srg74/WLED-wemos-shield/resources/Add-ons/ics-43434/ics43434_shield.jpg

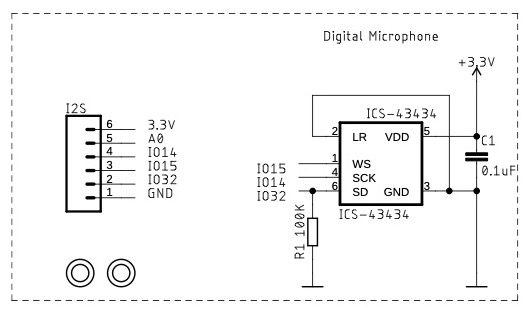
resources/Add-ons/ics-43434/ics43434_shield.jpg
