srg74/WLED-wemos-shield/resources/Add-ons/linear_input/Sound_reactive_add-on.png

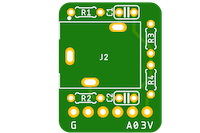
resources/Add-ons/linear_input/Sound_reactive_add-on.png
