srg74/WLED-wemos-shield/resources/Images/esp32-esp8266.jpg

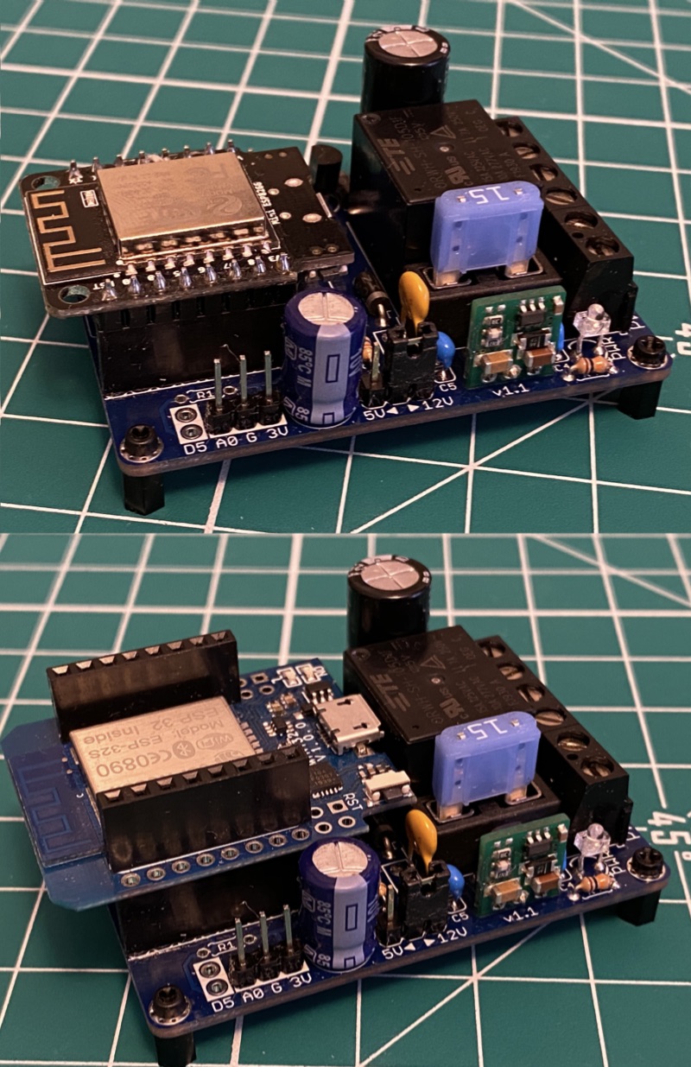
resources/Images/esp32-esp8266.jpg
