srg74/WLED-wemos-shield/resources/Images/ESP32_d1.jpeg

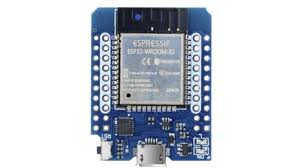
resources/Images/ESP32_d1.jpeg
