srg74/WLED-wemos-shield/resources/Images/Flasher1.png

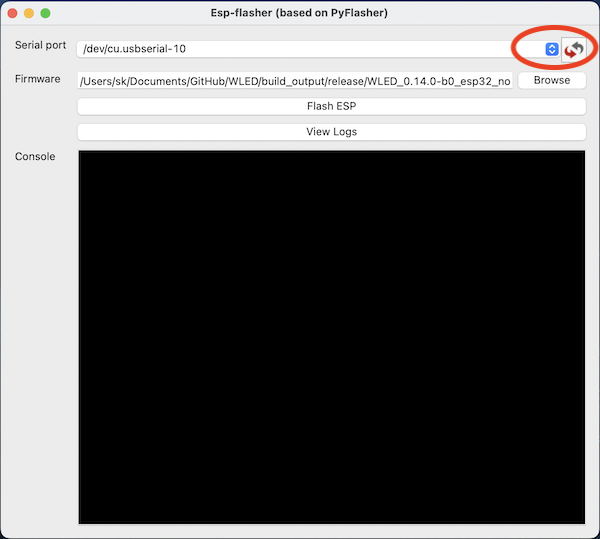
resources/Images/Flasher1.png
