srg74/WLED-wemos-shield/resources/Images/Flasher4.png

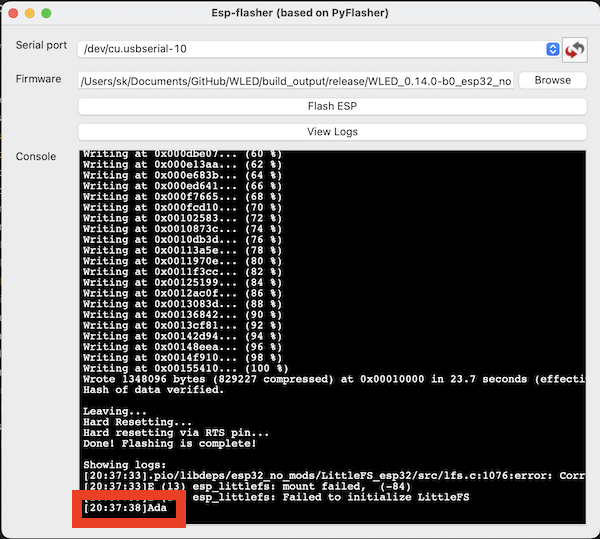
resources/Images/Flasher4.png
