srg74/WLED-wemos-shield/resources/Images/H803FW.jpg

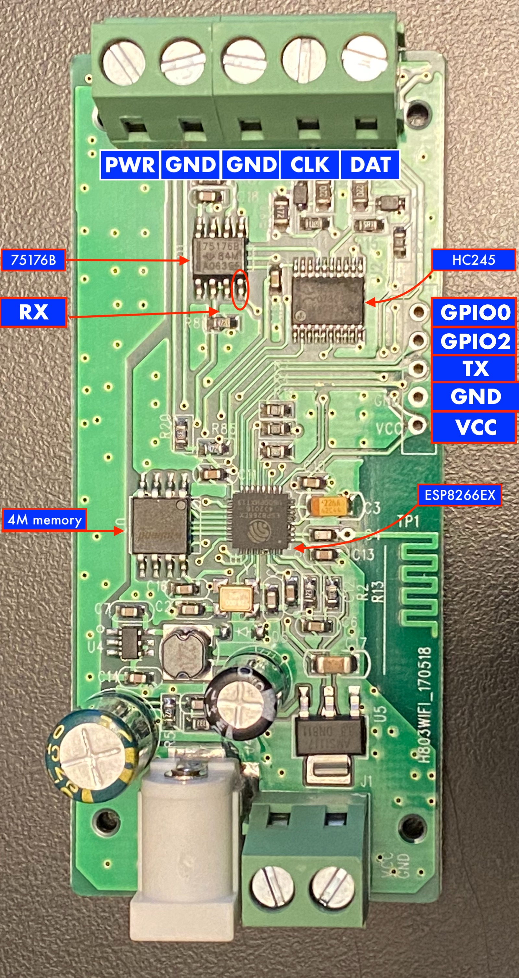
resources/Images/H803FW.jpg
