srg74/WLED-wemos-shield/resources/Images/Lilygo_TTGO_v1.3.jpeg

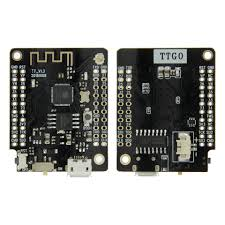
resources/Images/Lilygo_TTGO_v1.3.jpeg
