srg74/WLED-wemos-shield/resources/Images/mini.jpeg

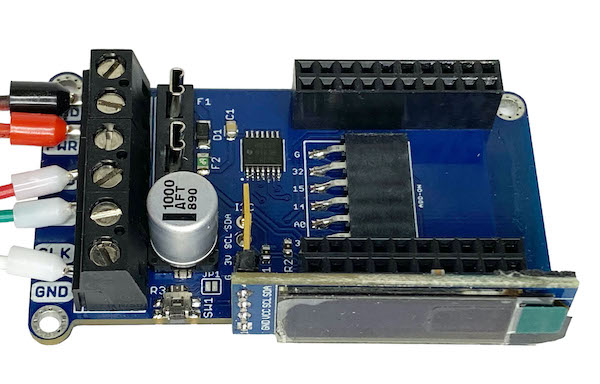
resources/Images/mini.jpeg
