srg74/WLED-wemos-shield/resources/Images/overview.jpg

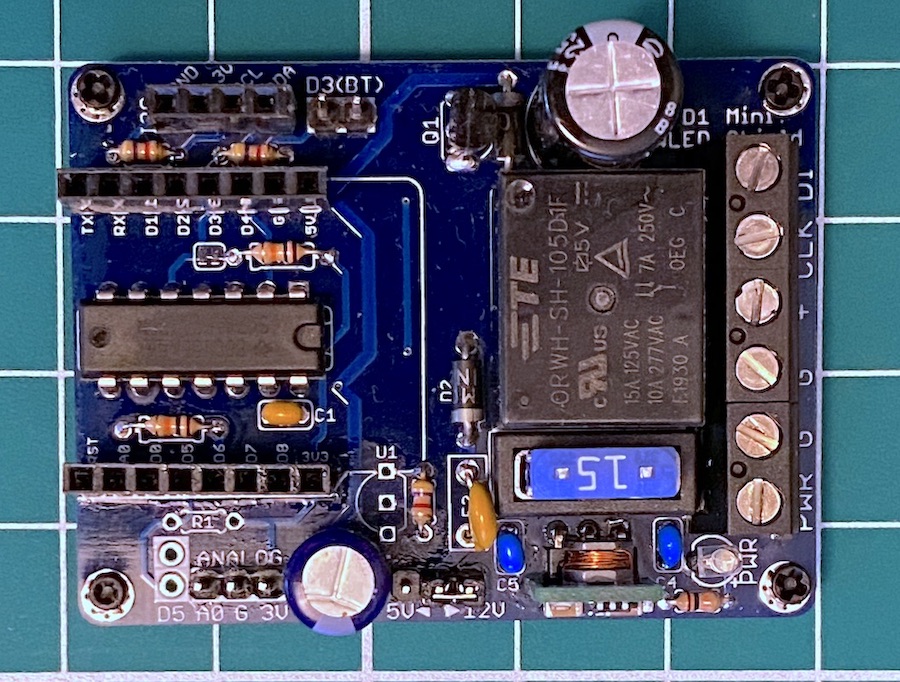
resources/Images/overview.jpg
