srg74/WLED-wemos-shield/resources/Images/Shield_v1.5-3D.png

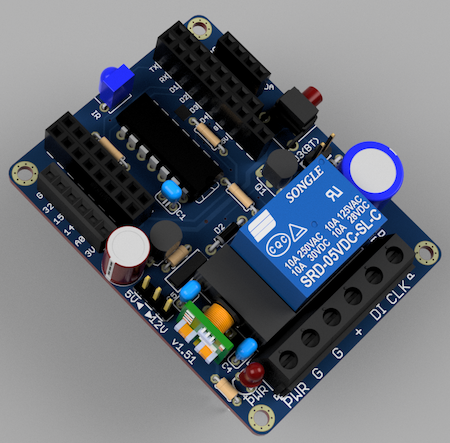
resources/Images/Shield_v1.5-3D.png
