srg74/WLED-wemos-shield/resources/Images/Variant_1.jpg

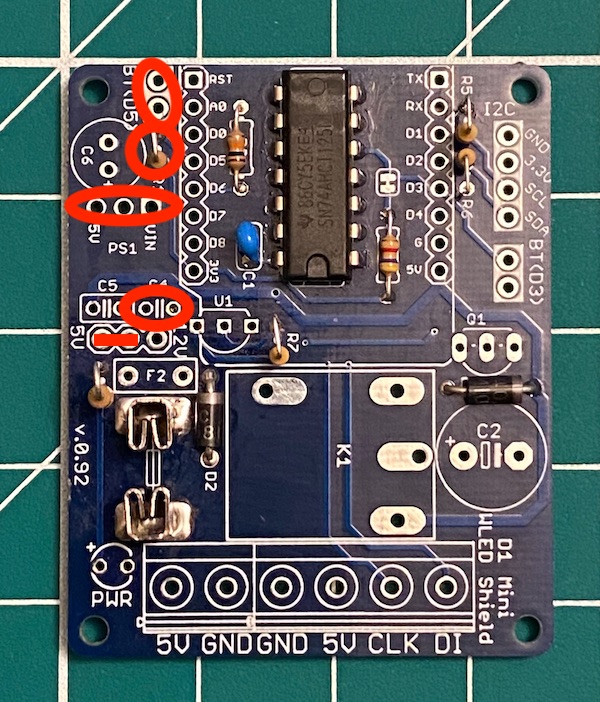
resources/Images/Variant_1.jpg
