srg74/WLED-wemos-shield/resources/Images/Variant_2.jpg

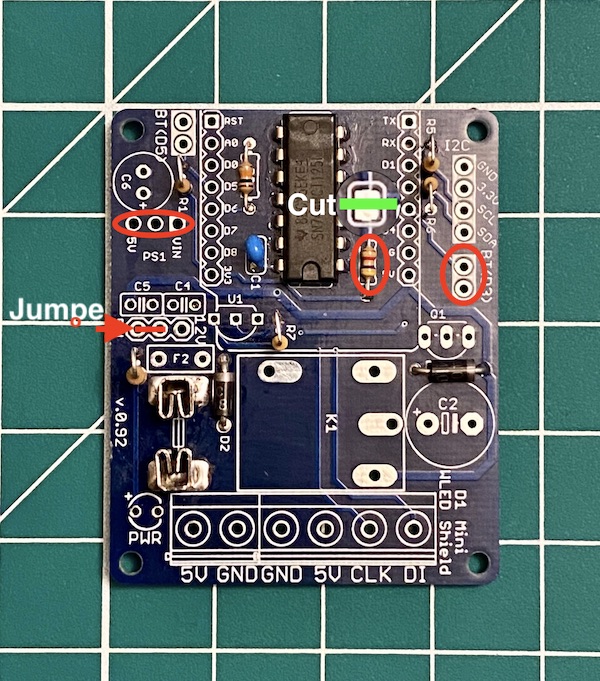
resources/Images/Variant_2.jpg
