srg74/WLED-wemos-shield/resources/Images/Variant_3.jpg

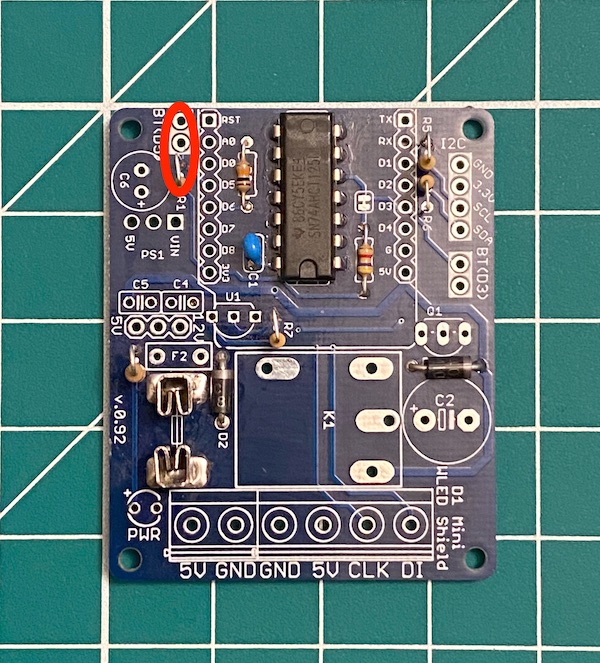
resources/Images/Variant_3.jpg
