srg74/WLED-wemos-shield/resources/Images/Wemos_clone.jpg

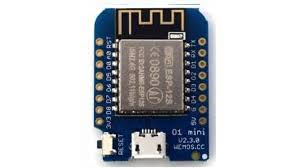
resources/Images/Wemos_clone.jpg
