srg74/WLED-wemos-shield/resources/Images/Wemos_orig.jpg

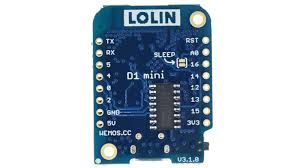
resources/Images/Wemos_orig.jpg
