srg74/WLED-wemos-shield/resources/Images/Wemos_set.jpg

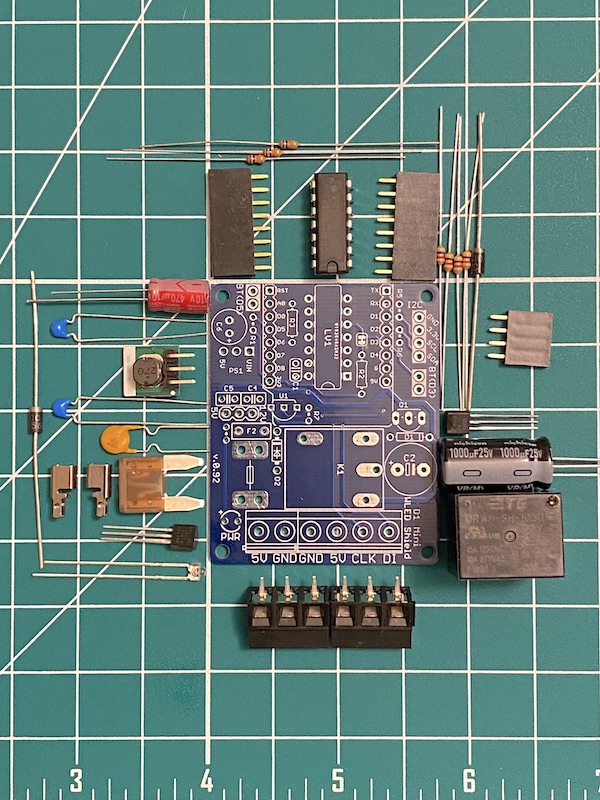
resources/Images/Wemos_set.jpg
