srg74/WLED-wemos-shield/resources/Images/wiki/board-powered.jpg

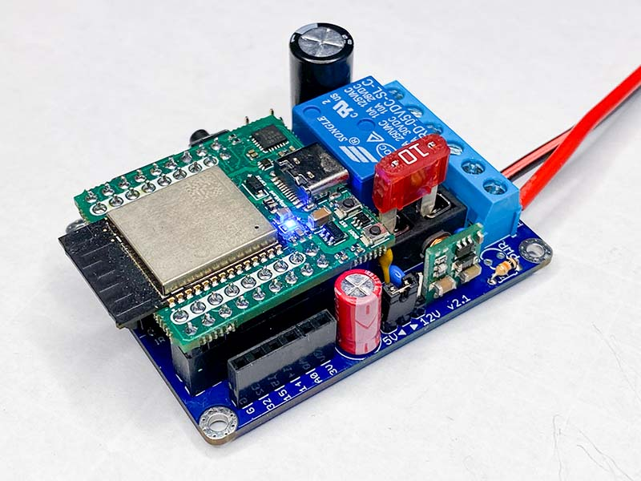
resources/Images/wiki/board-powered.jpg
