srg74/WLED-wemos-shield/resources/Images/wiki/board.jpg

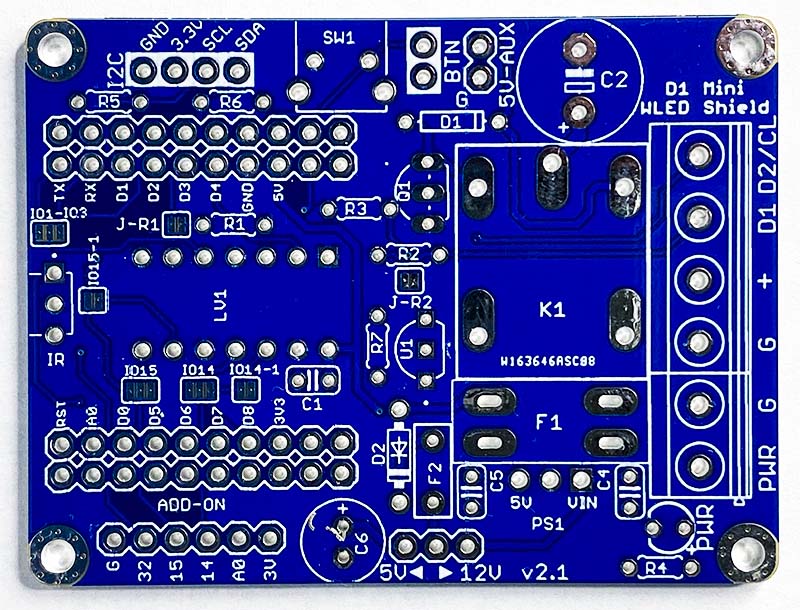
resources/Images/wiki/board.jpg
