srg74/WLED-wemos-shield/resources/Images/wiki/ESP32_mini_board1.png

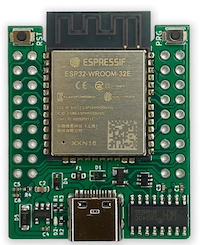
resources/Images/wiki/ESP32_mini_board1.png
