srg74/WLED-wemos-shield/resources/Images/wiki/jumper-set.jpg

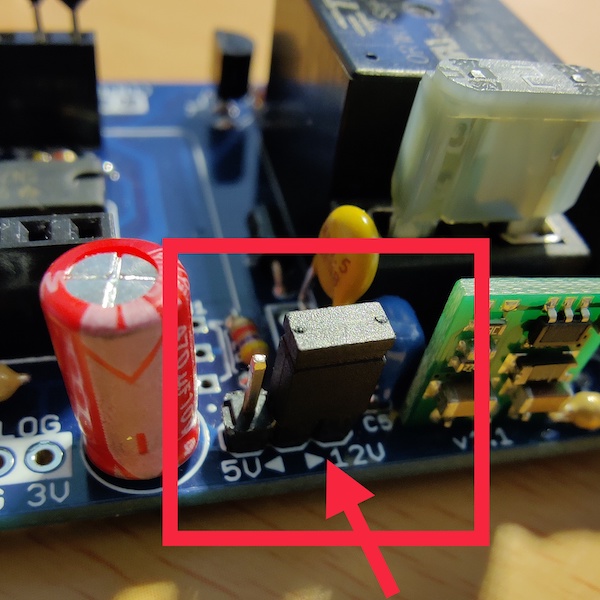
resources/Images/wiki/jumper-set.jpg
