srg74/WLED-wemos-shield/resources/Images/wiki/minimum-set.jpg

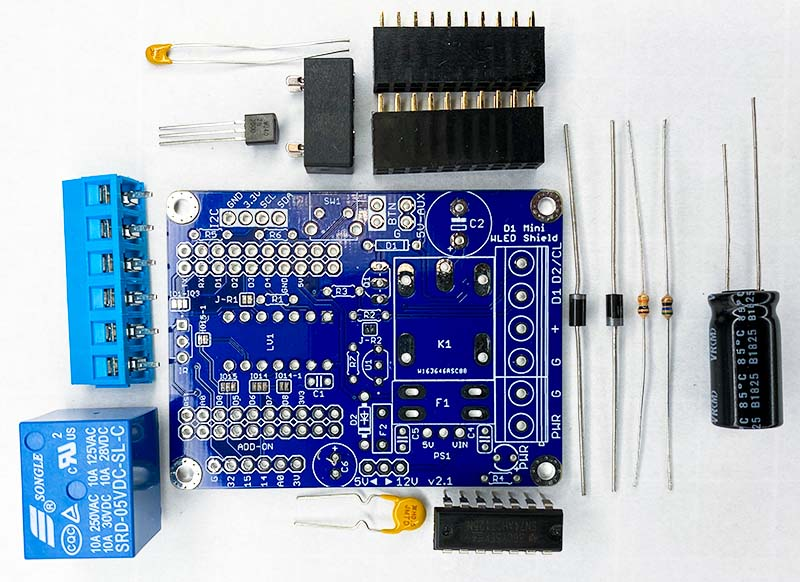
resources/Images/wiki/minimum-set.jpg
