srg74/WLED-wemos-shield/resources/Images/wiki/no-jumper.jpg

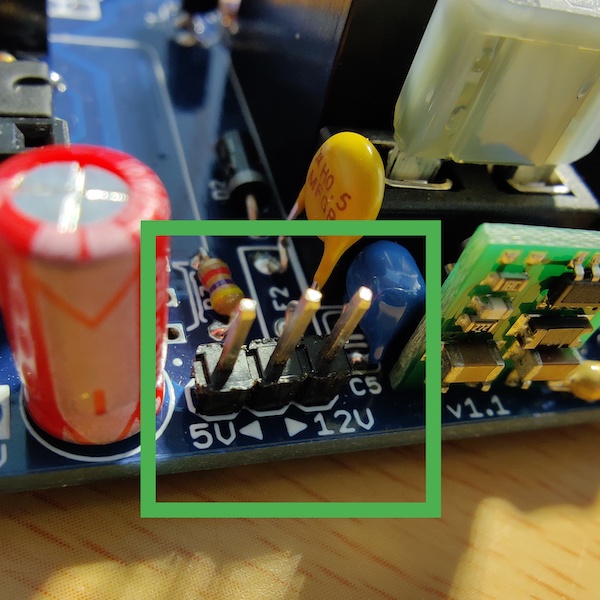
resources/Images/wiki/no-jumper.jpg
