srg74/WLED-wemos-shield/resources/Images/wiki/placement1.jpg

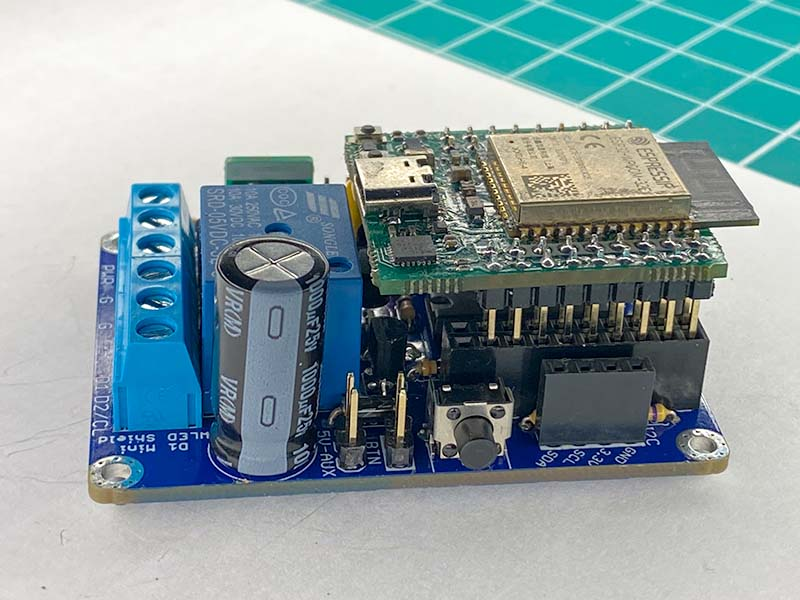
resources/Images/wiki/placement1.jpg
