srg74/WLED-wemos-shield/resources/Images/wiki/placement2.jpg

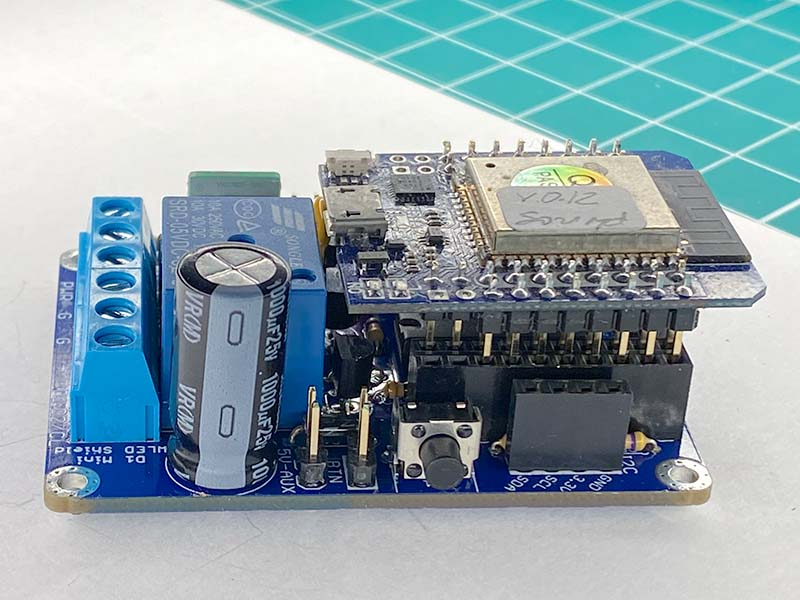
resources/Images/wiki/placement2.jpg
