srg74/WLED-wemos-shield/resources/Images/wiki/placement3.jpg

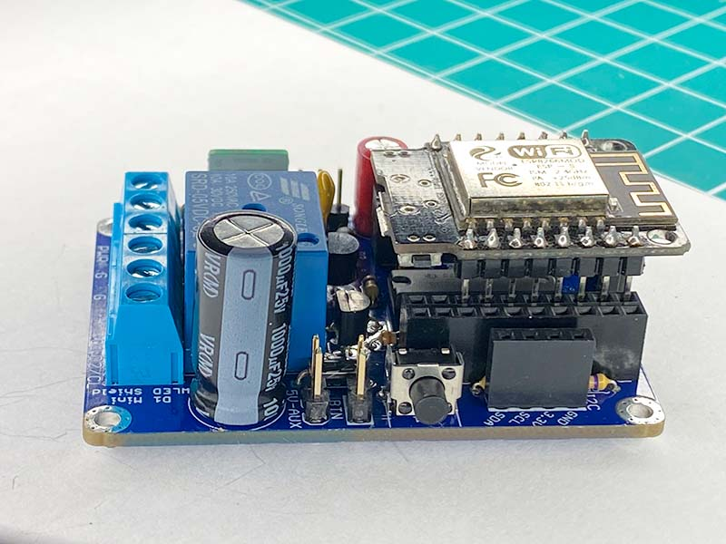
resources/Images/wiki/placement3.jpg
