srg74/WLED-wemos-shield/resources/Images/wiki/Pretest.jpg

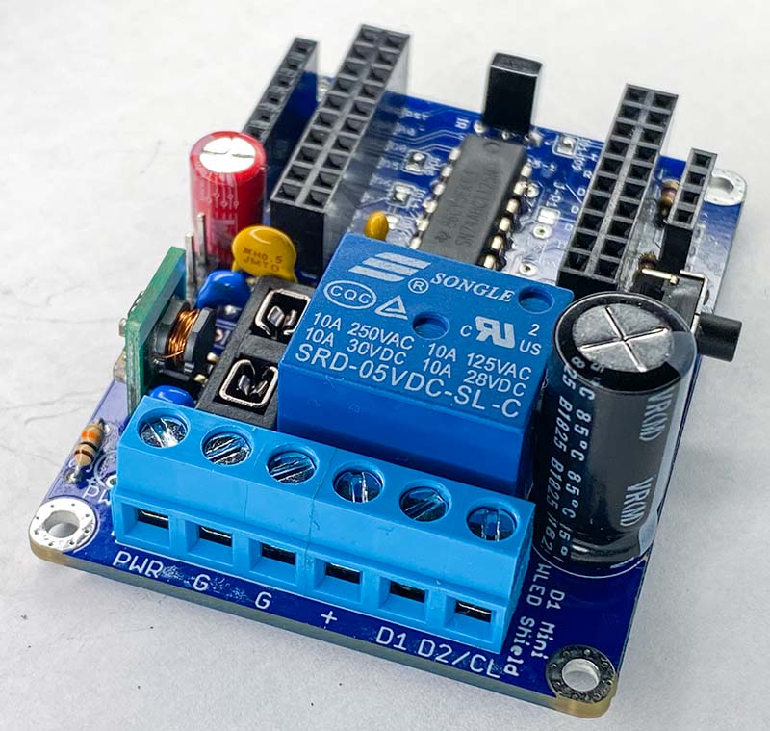
resources/Images/wiki/Pretest.jpg
