srg74/WLED-wemos-shield/resources/Images/wiki/QuinLED-ESP32-AE.png

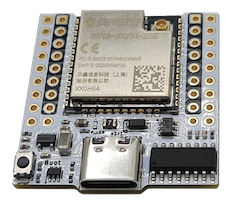
resources/Images/wiki/QuinLED-ESP32-AE.png
