srg74/WLED-wemos-shield/resources/Images/wiki/set-full.jpg

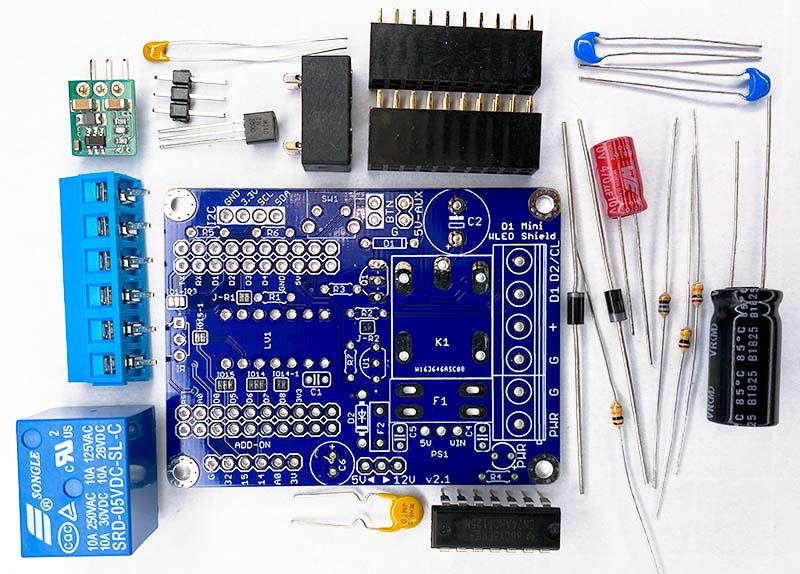
resources/Images/wiki/set-full.jpg
