srg74/WLED-wemos-shield/resources/Images/wiki/Wemos_shield_pinout.jpg

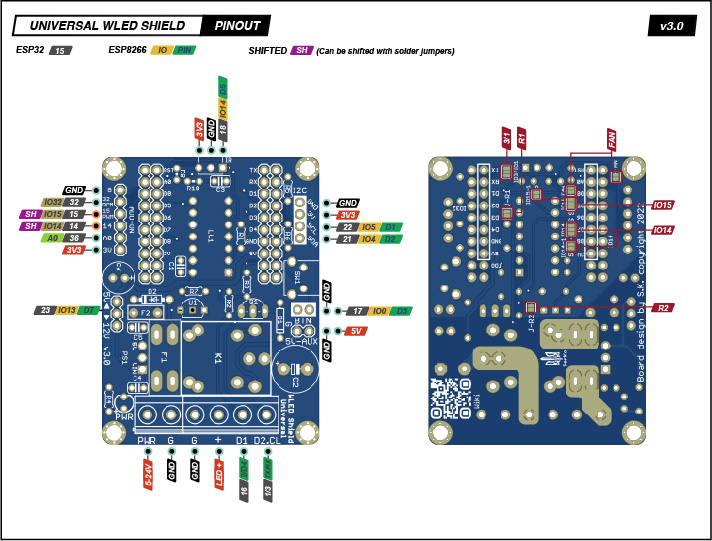
resources/Images/wiki/Wemos_shield_pinout.jpg
