srg74/WLED-wemos-shield/resources/Images/wiki/WLED_Wemos_bottom.png

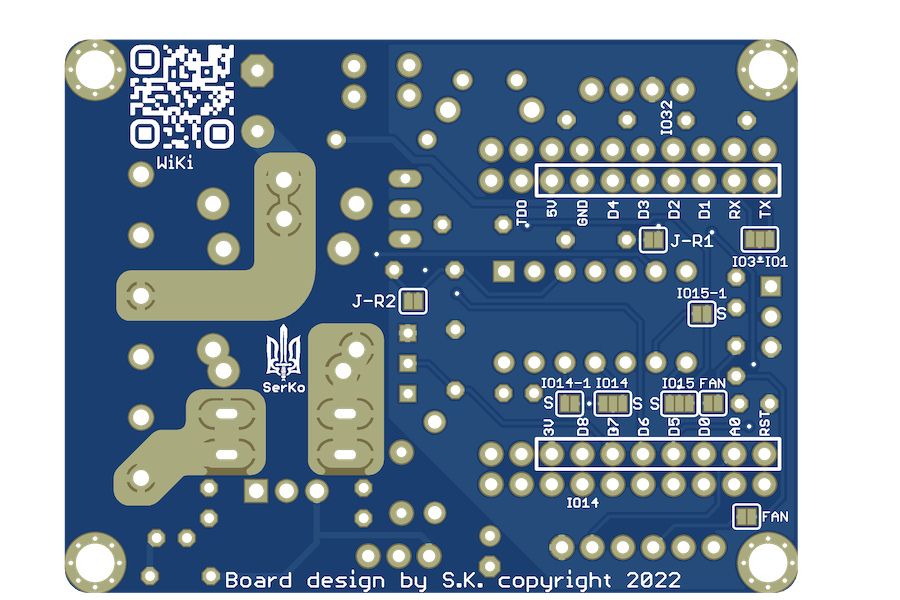
resources/Images/wiki/WLED_Wemos_bottom.png
