srg74/WLED-wemos-shield/resources/Images/Assembly_2.jpg

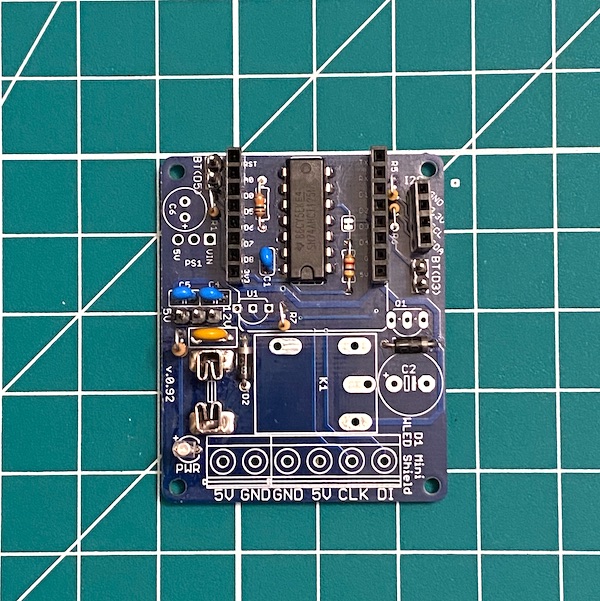
resources/Images/Assembly_2.jpg
