srg74/WLED-wemos-shield/resources/Images/Assembly_3.jpg

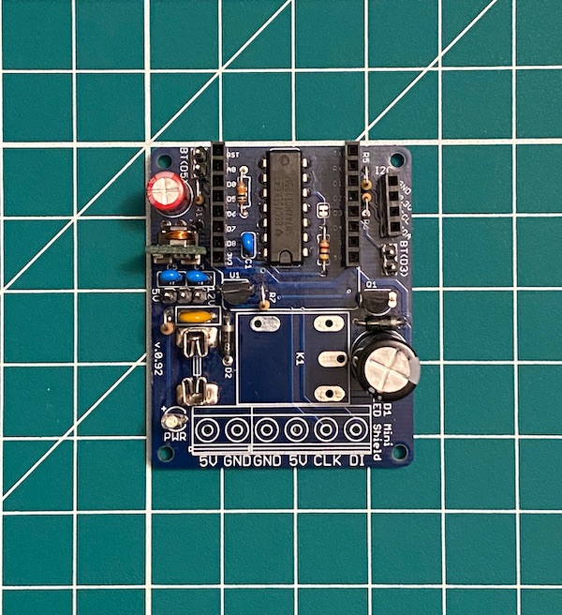
resources/Images/Assembly_3.jpg
