srg74/WLED-wemos-shield/resources/Images/Assembly_4.jpg

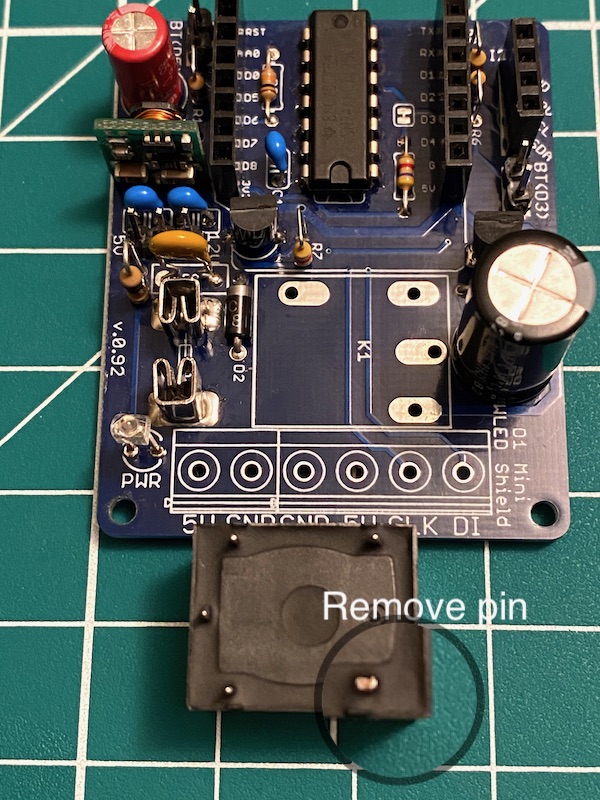
resources/Images/Assembly_4.jpg
