srg74/WLED-wemos-shield/resources/Images/Assembly_4a.jpg

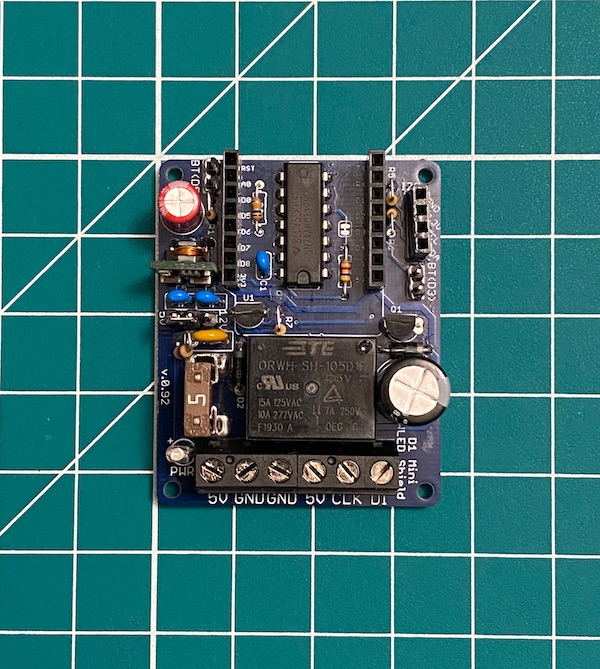
resources/Images/Assembly_4a.jpg
