srg74/WLED-wemos-shield/resources/Images/Assembly_5.jpg

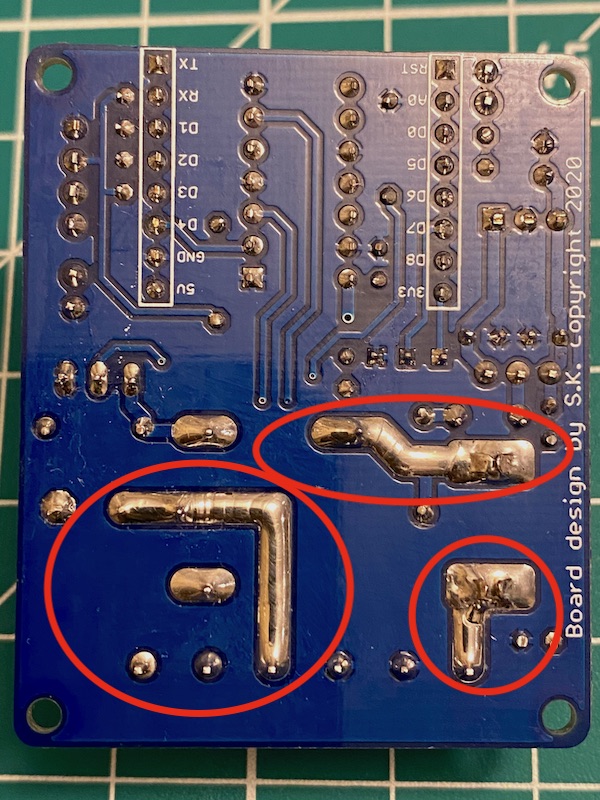
resources/Images/Assembly_5.jpg
