srg74/WLED-wemos-shield/resources/Images/Assembly_6.jpg

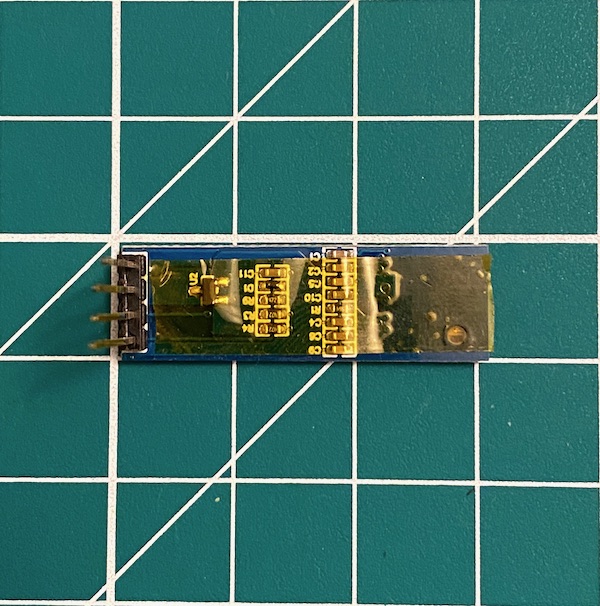
resources/Images/Assembly_6.jpg
