srg74/WLED-wemos-shield/resources/Images/Assembly_8.jpg

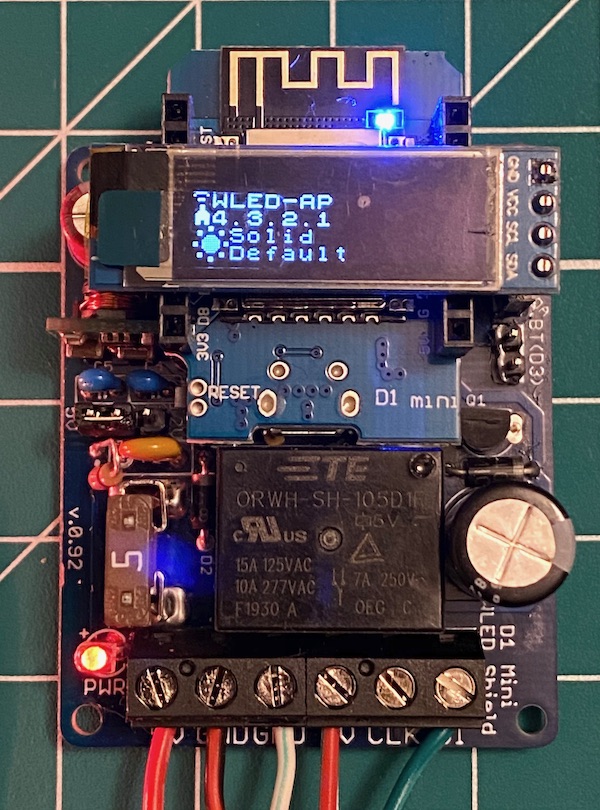
resources/Images/Assembly_8.jpg
