srg74/WLED-wemos-shield/resources/Images/wiki/solder-traces.png

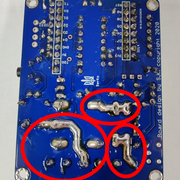
resources/Images/wiki/solder-traces.png
