srg74/WLED-wemos-shield/resources/Images/wiki/step2.jpg

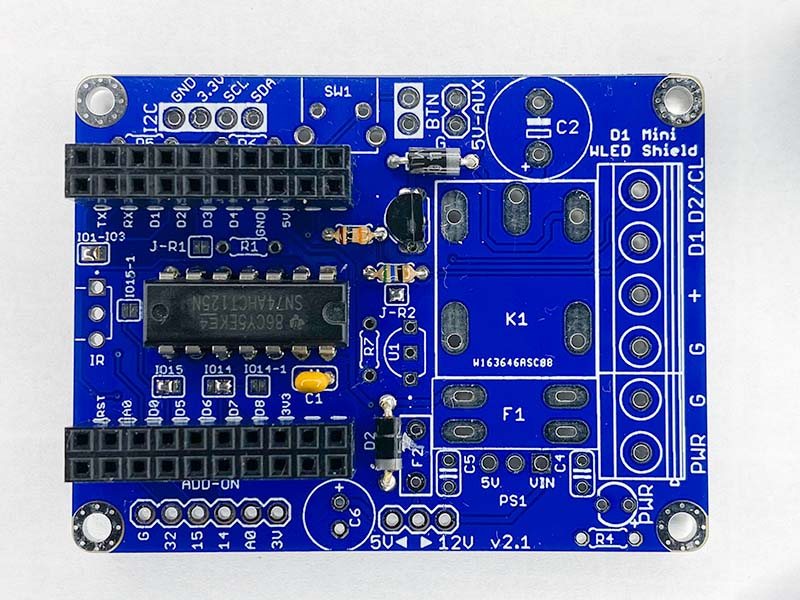
resources/Images/wiki/step2.jpg
