srg74/WLED-wemos-shield/resources/Images/wiki/step3.jpg

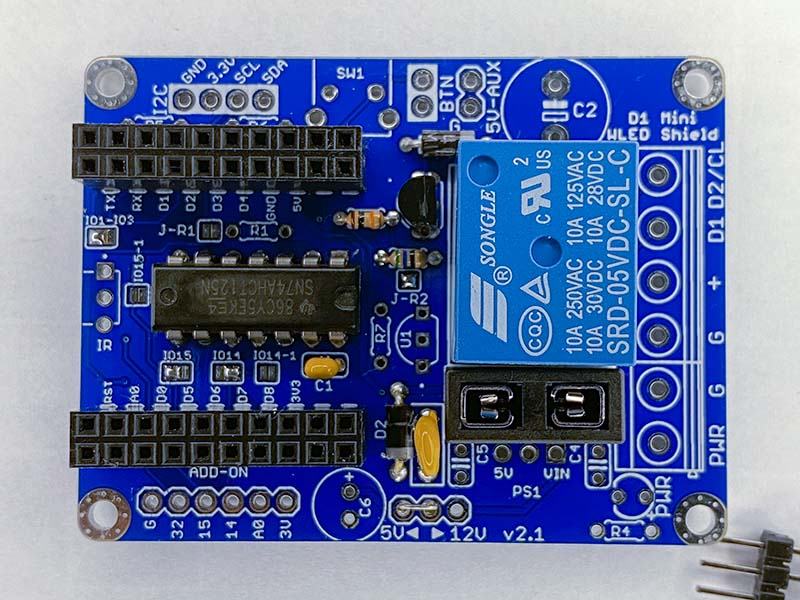
resources/Images/wiki/step3.jpg
