srg74/WLED-wemos-shield/resources/Images/wiki/step5.jpg

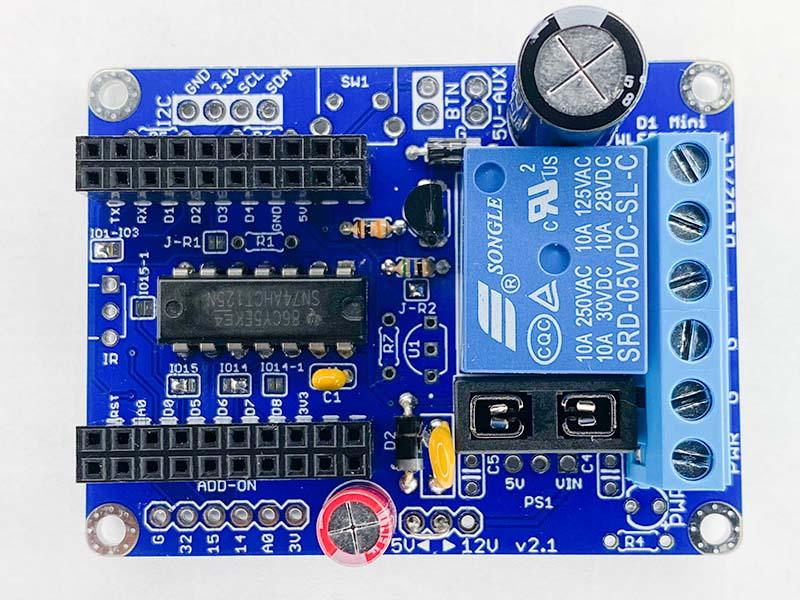
resources/Images/wiki/step5.jpg
