srg74/WLED-wemos-shield/resources/Images/wiki/step6.jpg

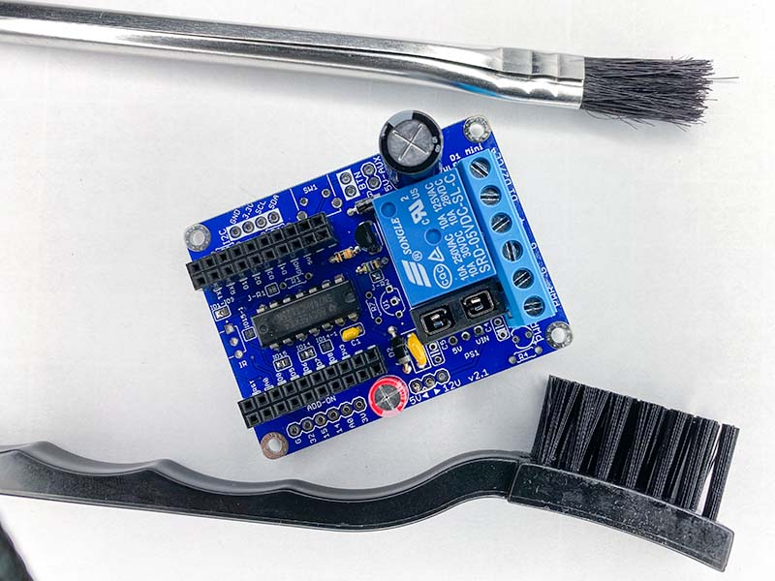
resources/Images/wiki/step6.jpg
