srg74/WLED-wemos-shield/resources/Images/wiki/test1.jpg

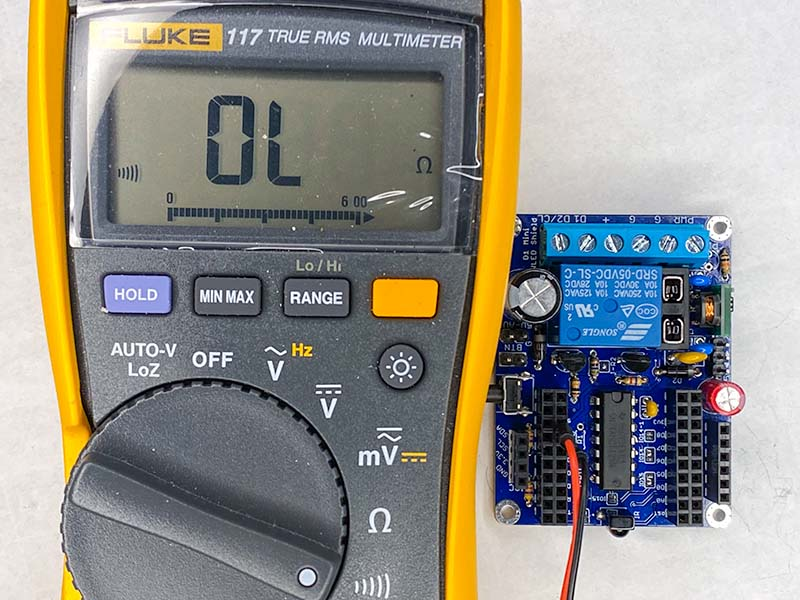
resources/Images/wiki/test1.jpg
