srg74/WLED-wemos-shield/resources/Images/wiki/test2.jpg

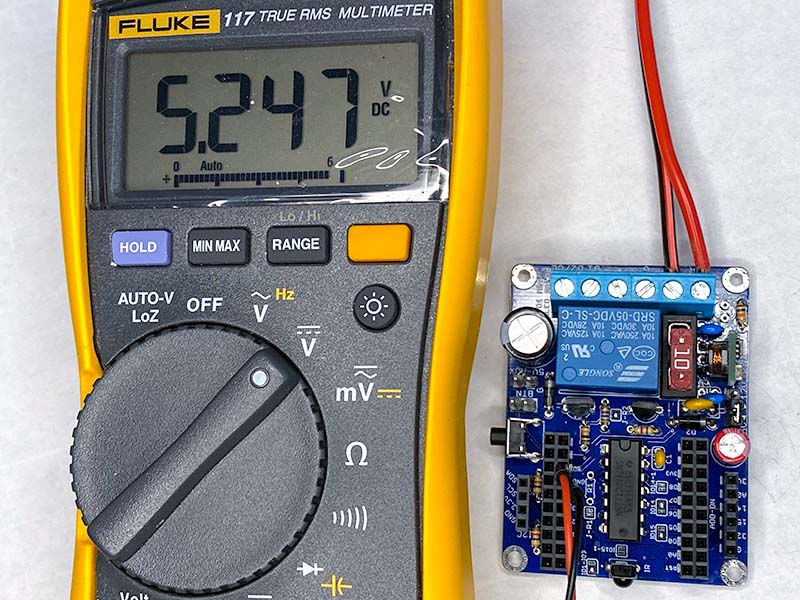
resources/Images/wiki/test2.jpg
